wiciu15/STM32-USBHID-MultimediaPilot/PCB/MultimediaPilot.sch

## KiCad design PCB/MultimediaPilot.sch (2020-03-15)

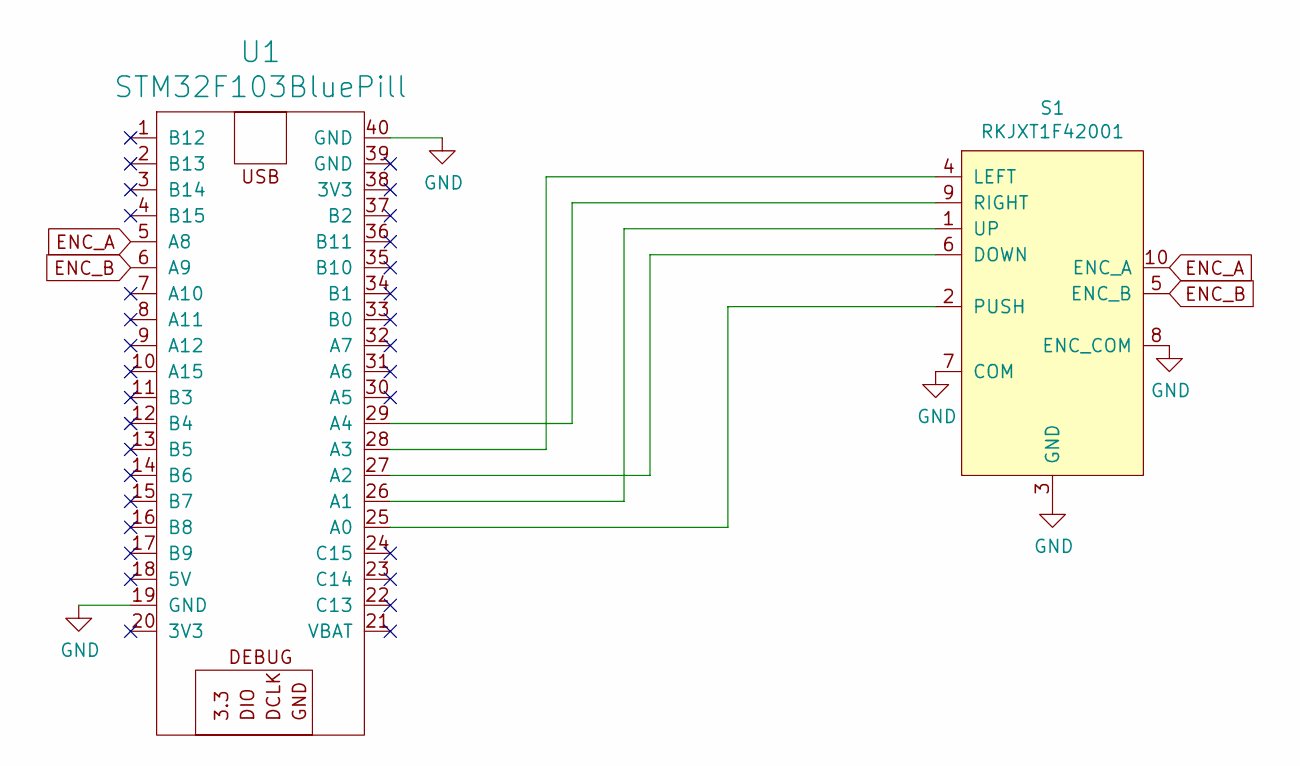
[picture p12: schematic MultimediaPilot.sch]

Parts:
S1: RKJXT1F42001
U1: STM32F103BluePill

Connections:
ENC_A: S1.10 (ENC_A), U1.5 (A8)
ENC_B: S1.5 (ENC_B), U1.6 (A9)
GND: S1.3 (GND), S1.7 (COM), S1.8 (ENC_COM), U1.19 (GND), U1.40 (GND)
unnamed: S1.1 (UP), U1.26 (A1)
unnamed: S1.2 (PUSH), U1.25 (A0)
unnamed: S1.4 (LEFT), U1.28 (A3)
unnamed: S1.6 (DOWN), U1.27 (A2)
unnamed: S1.9 (RIGHT), U1.29 (A4)
